AkBKukU/adam-psu/doc/Coleco_Adam_Schematics/image--000.png

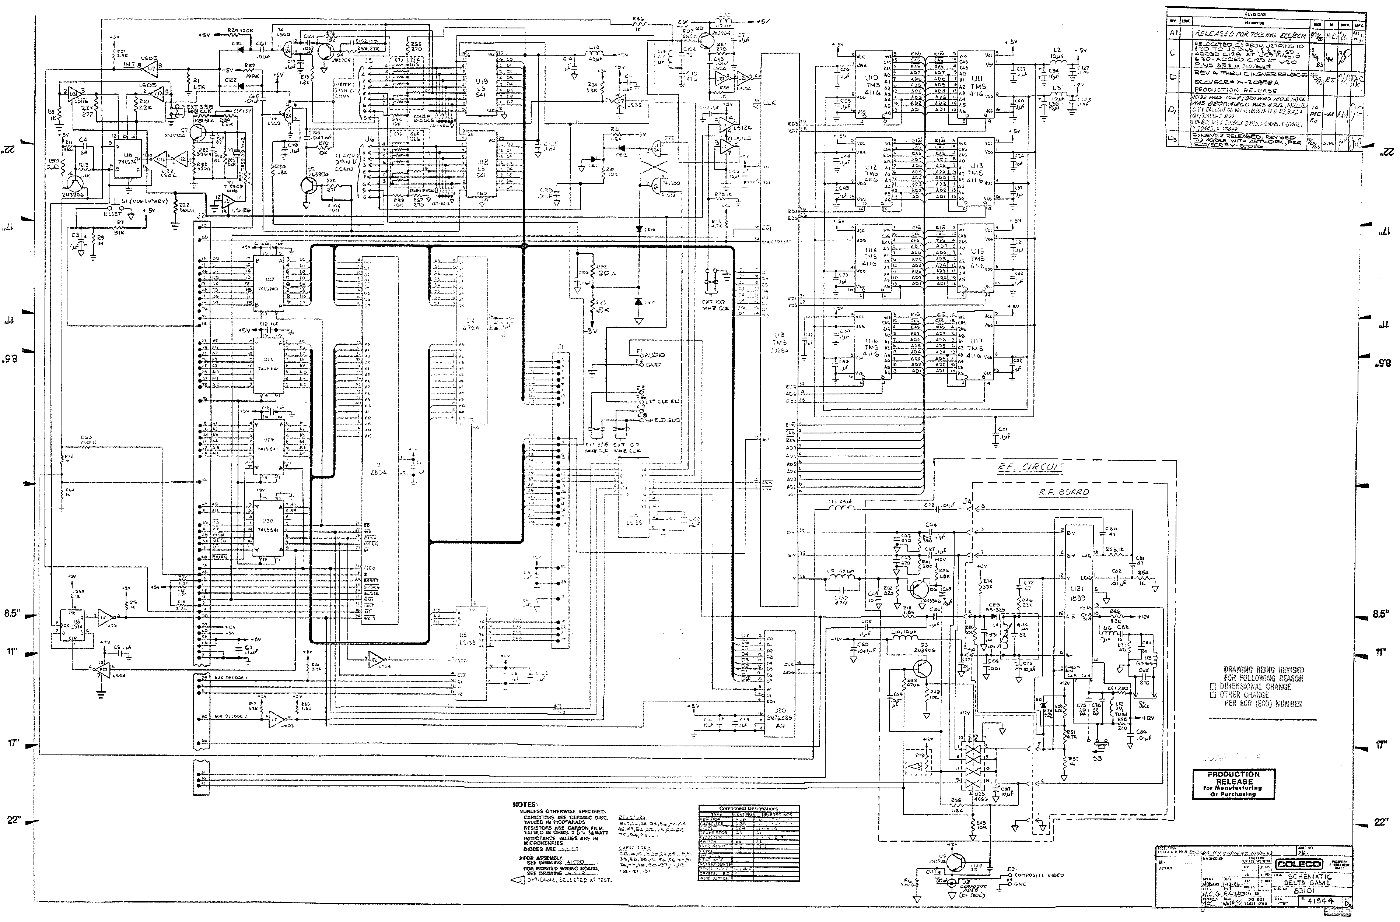
doc/Coleco_Adam_Schematics/image--000.png
