AkBKukU/adam-psu/doc/Coleco_Adam_Schematics/image--002.png

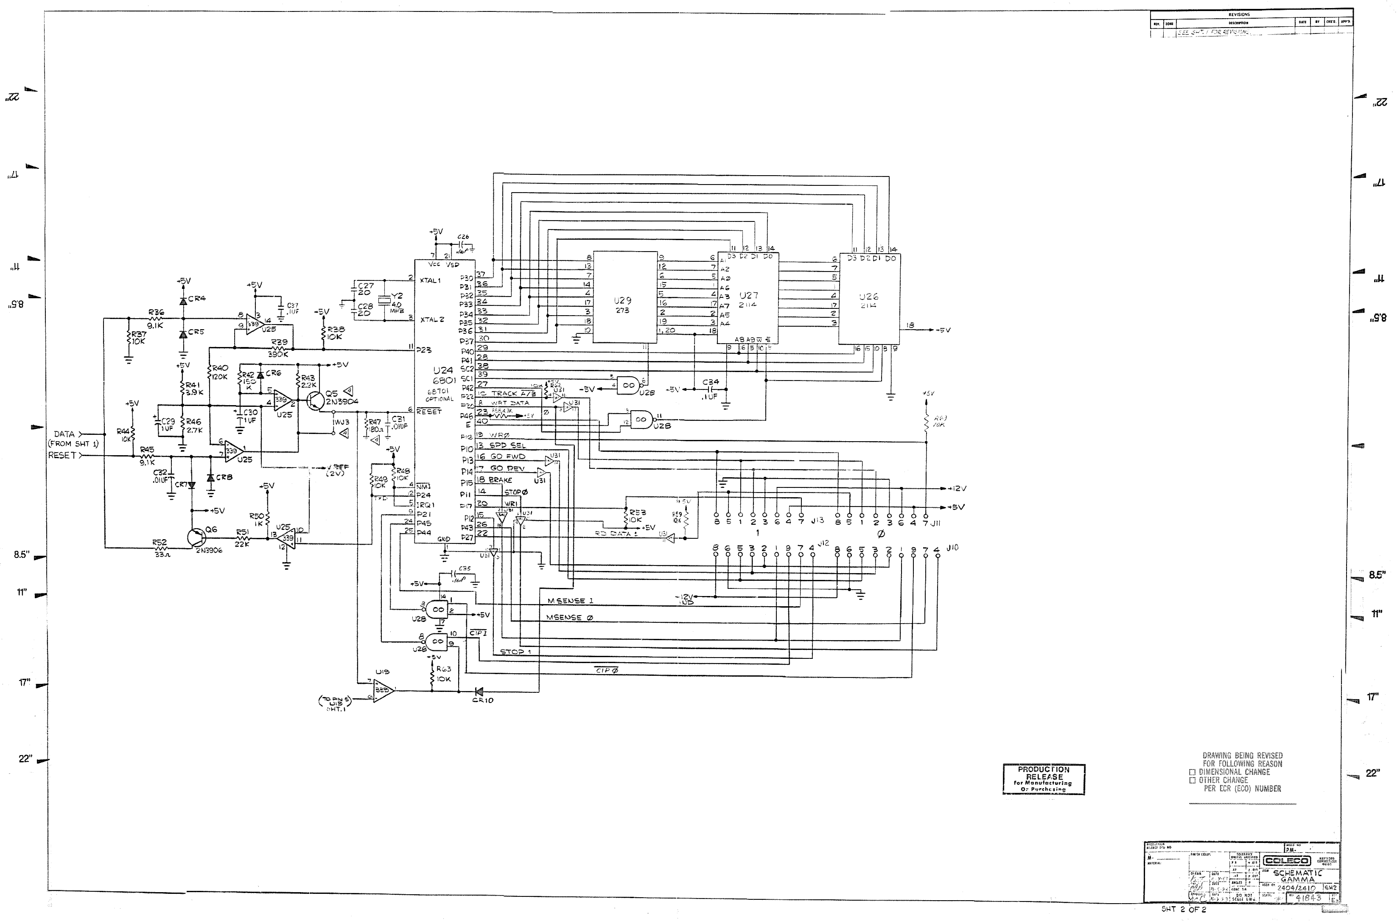
doc/Coleco_Adam_Schematics/image--002.png
