AkBKukU/adam-psu/doc/Coleco_Adam_Schematics/image--003.png

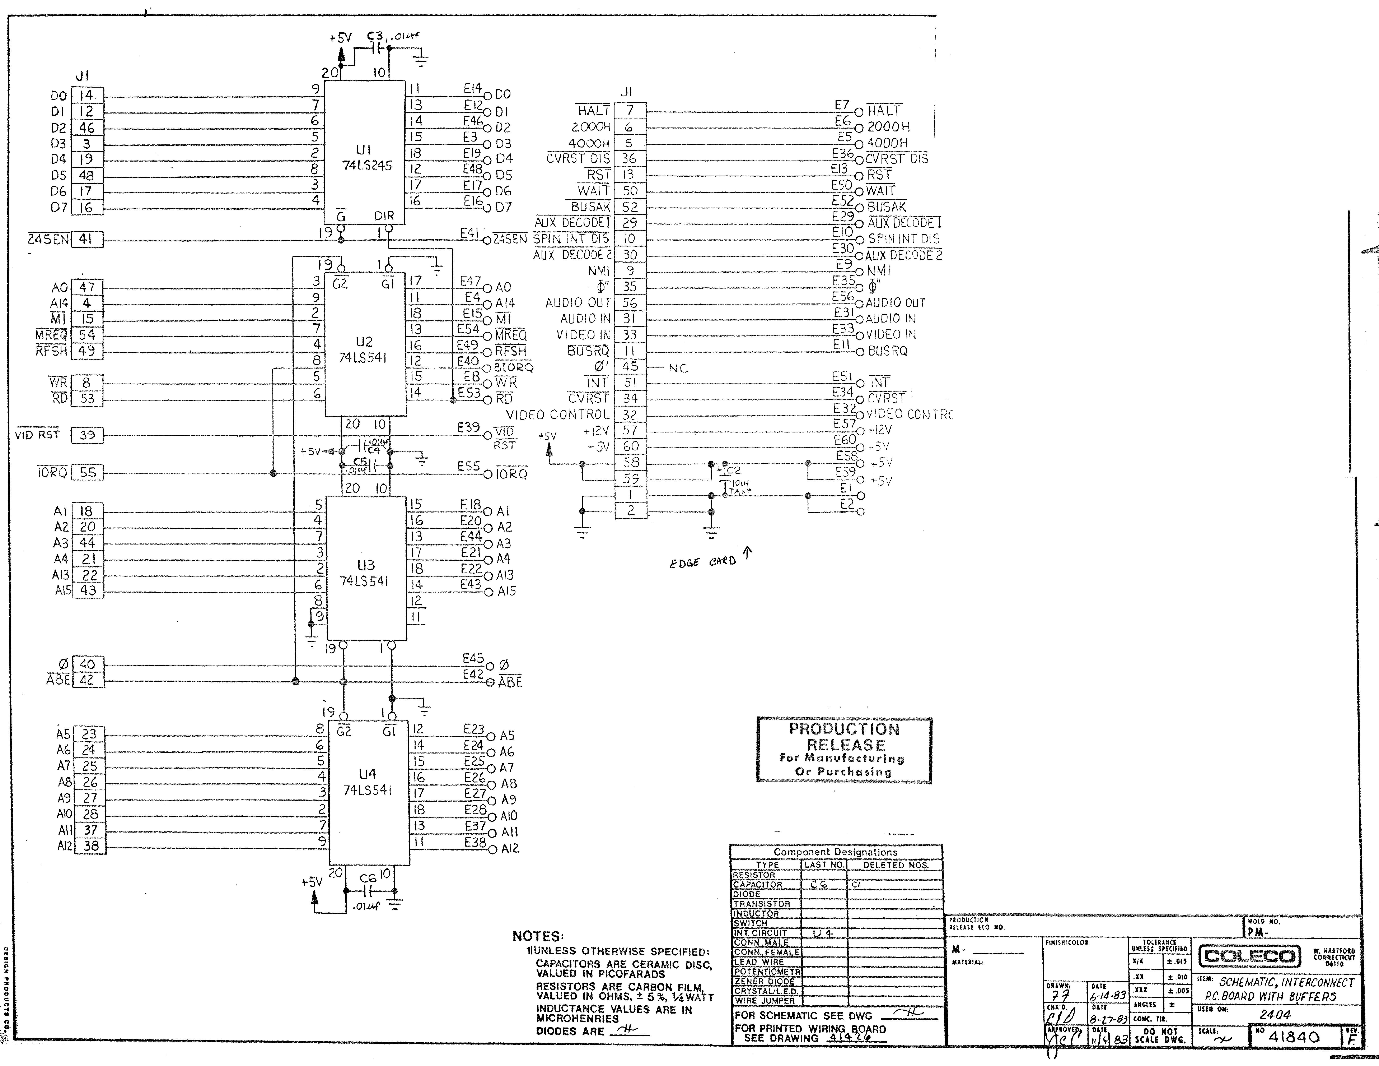
doc/Coleco_Adam_Schematics/image--003.png
