AkBKukU/adam-psu/doc/Coleco_Adam_Schematics/image--004.png

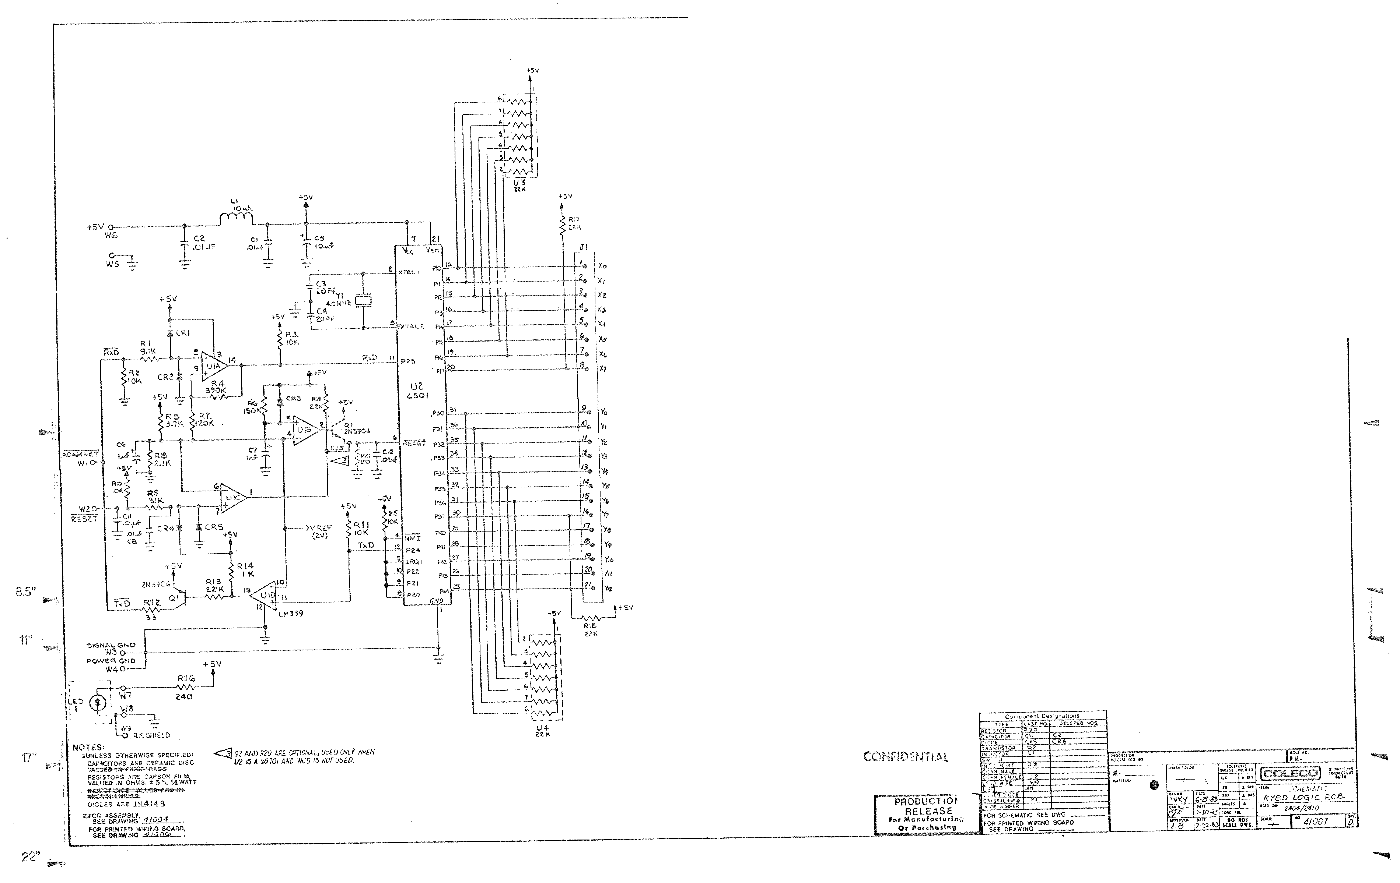
doc/Coleco_Adam_Schematics/image--004.png
