AkBKukU/adam-psu/doc/Coleco_Adam_Schematics/image--005.png

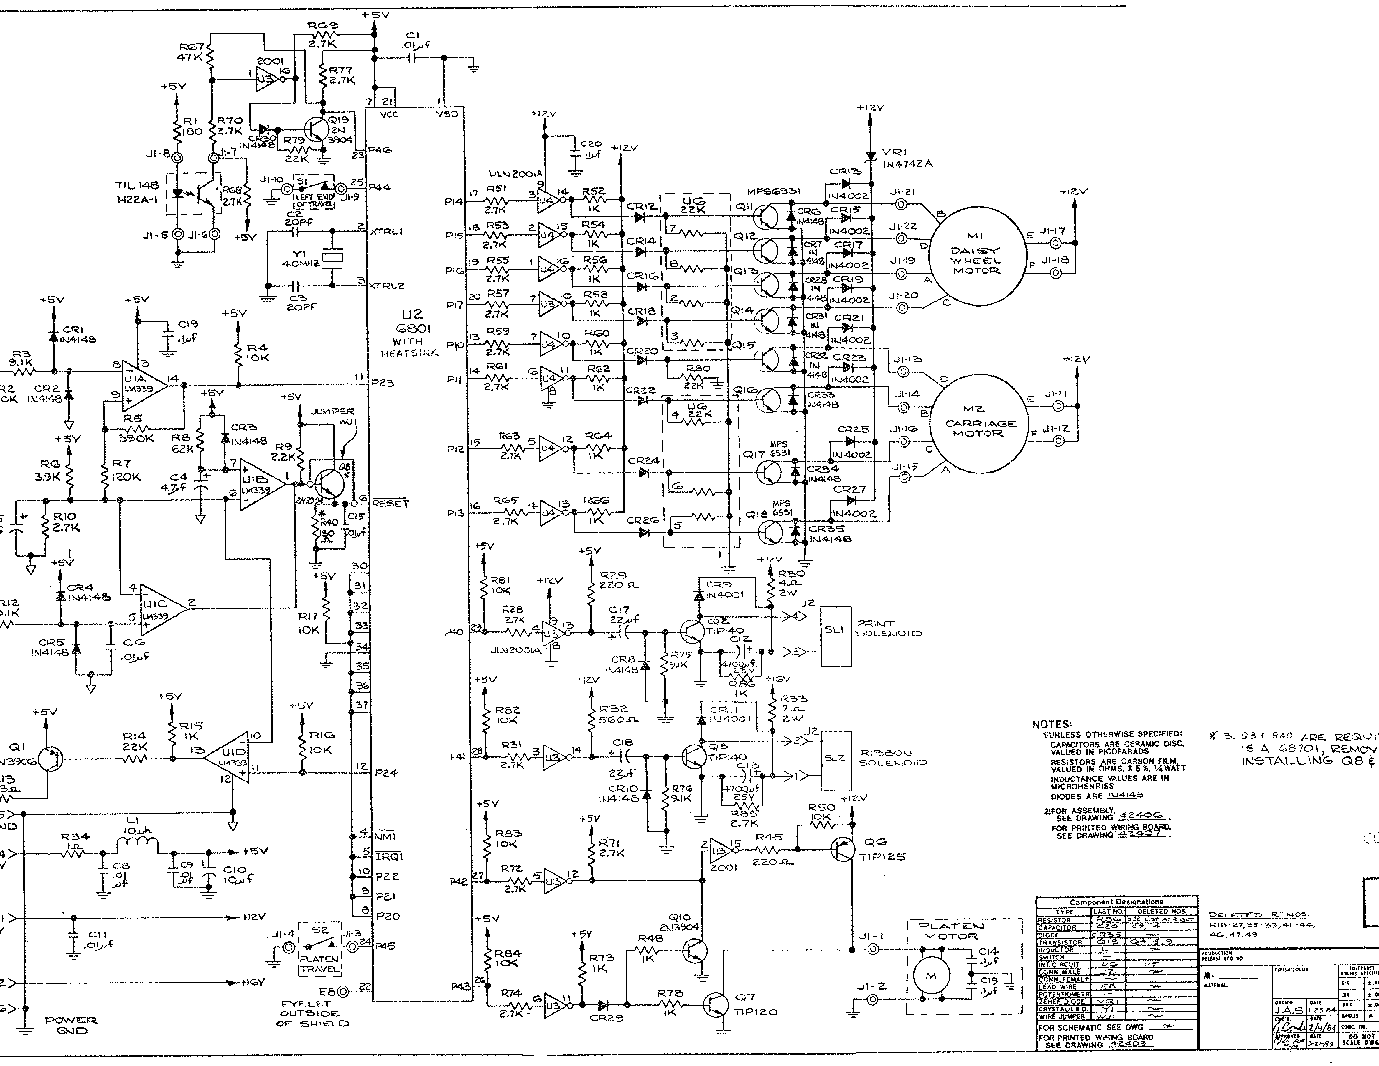
doc/Coleco_Adam_Schematics/image--005.png
