AkBKukU/adam-psu/doc/Coleco_Adam_Schematics/image--006.png

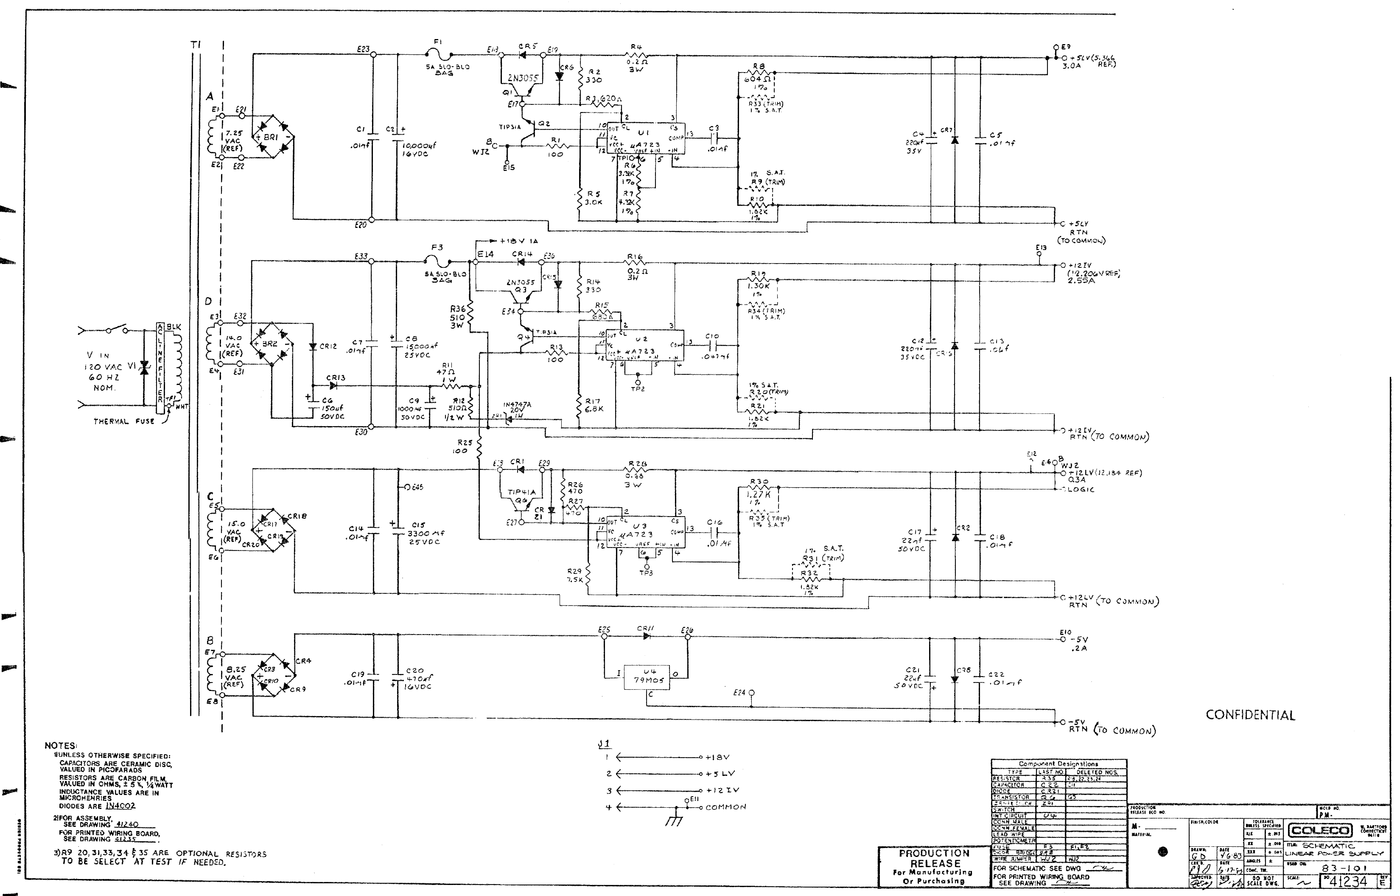
doc/Coleco_Adam_Schematics/image--006.png
