AkBKukU/adam-psu/doc/Coleco_Adam_Schematics/image--007.png

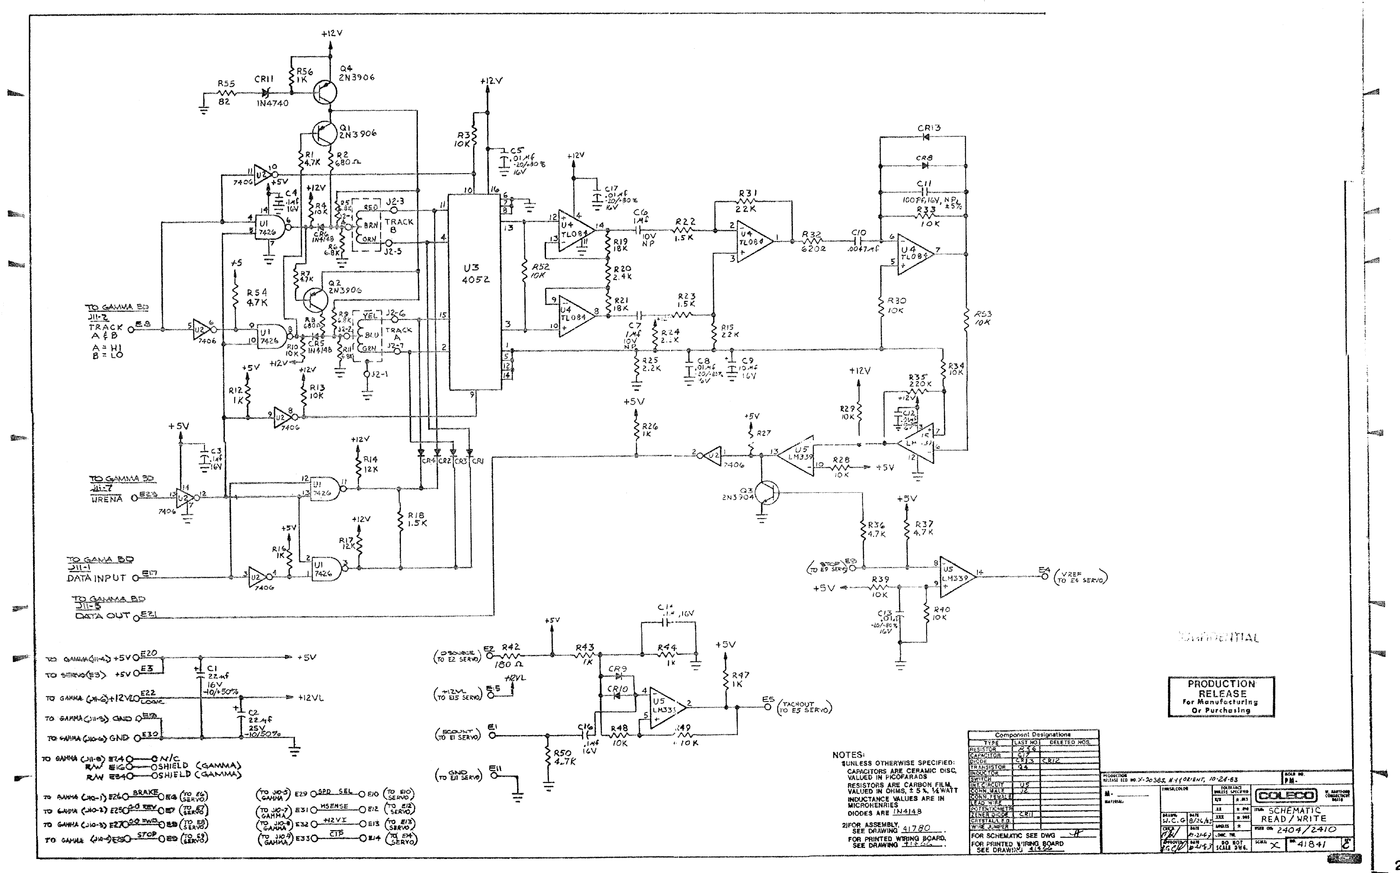
doc/Coleco_Adam_Schematics/image--007.png
