AkBKukU/adam-psu/doc/Coleco_Adam_Schematics/image--008.png

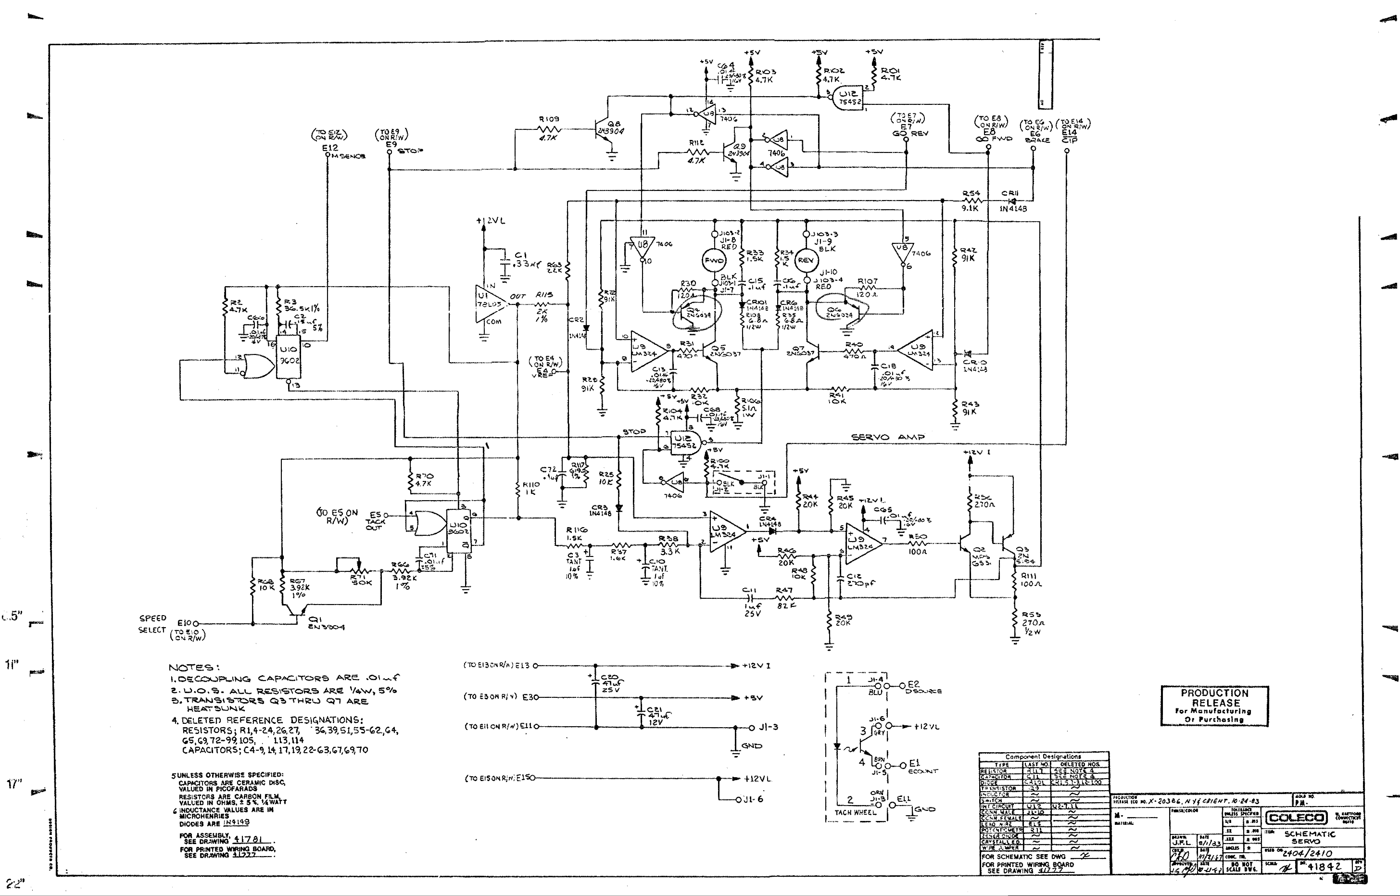
doc/Coleco_Adam_Schematics/image--008.png
